muccc/WomoLIN/Doc/freeplan/system_benutzerschnittstellen_v1.0.png

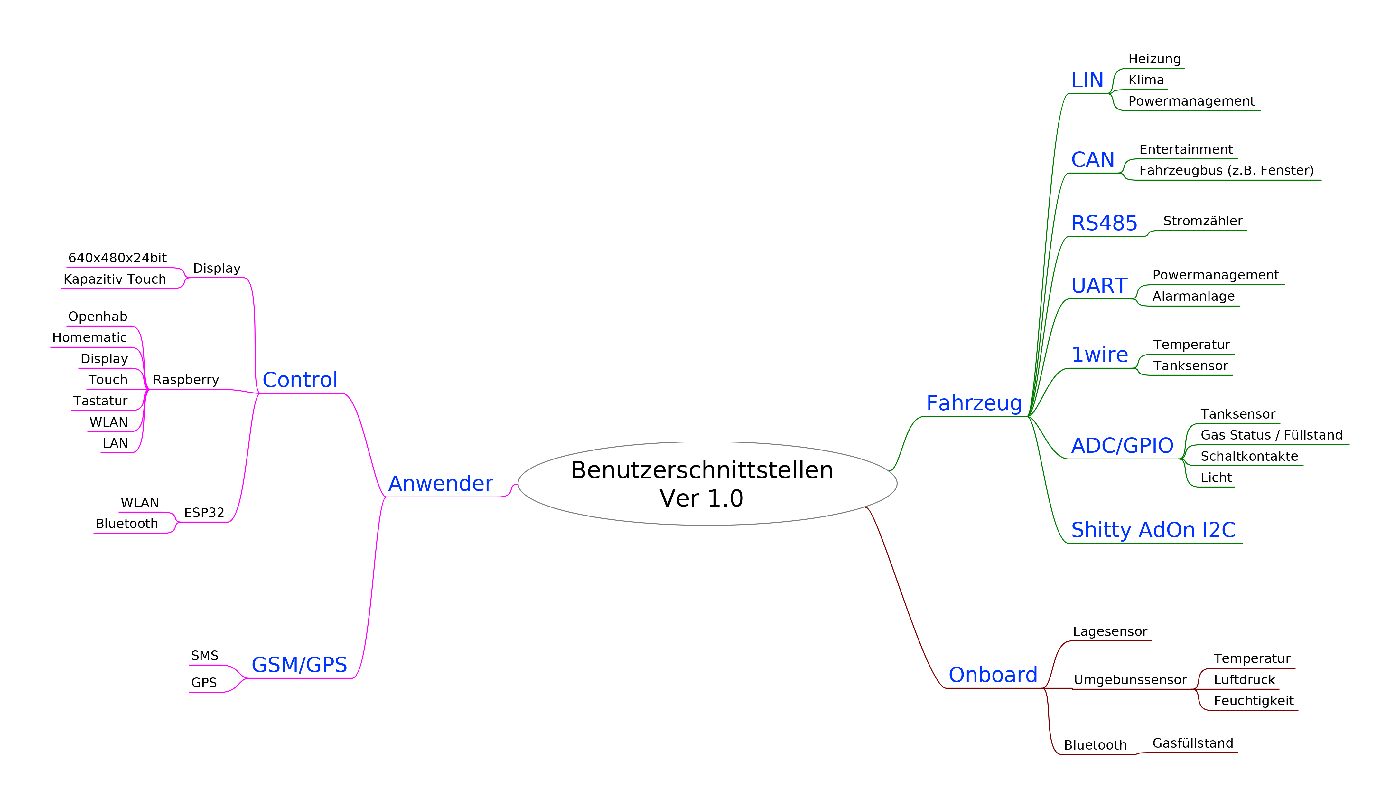
Doc/freeplan/system_benutzerschnittstellen_v1.0.png
