muccc/WomoLIN/Doc/pics/control_sensorboard_cutted.jpg

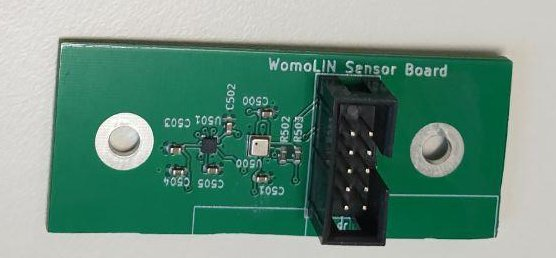
Doc/pics/control_sensorboard_cutted.jpg
