muccc/WomoLIN/Doc/pics/controlboard_2.0_steckverbinder.jpg

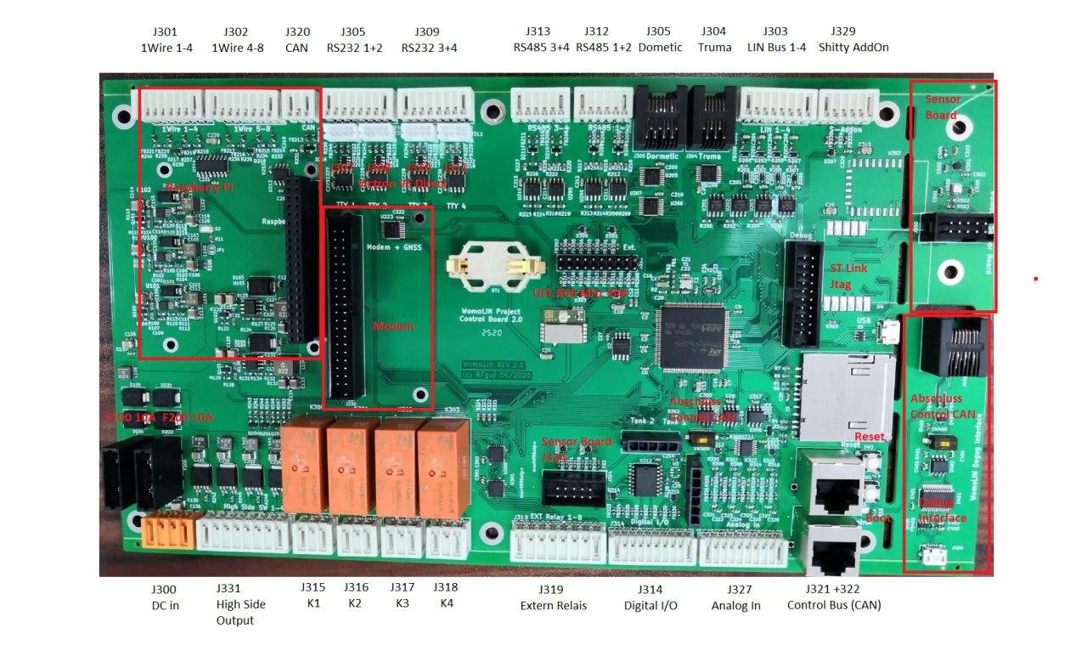
Doc/pics/controlboard_2.0_steckverbinder.jpg
