muccc/WomoLIN/Hardware/Biblotheken/WAGO/3D-Modelle/WAGO Klemmleisten Hebel/WAGO_Klemmleiste_Hebel4Vertikal_RM5mm_2-10-pol/2604-3106/2604-3106.stp

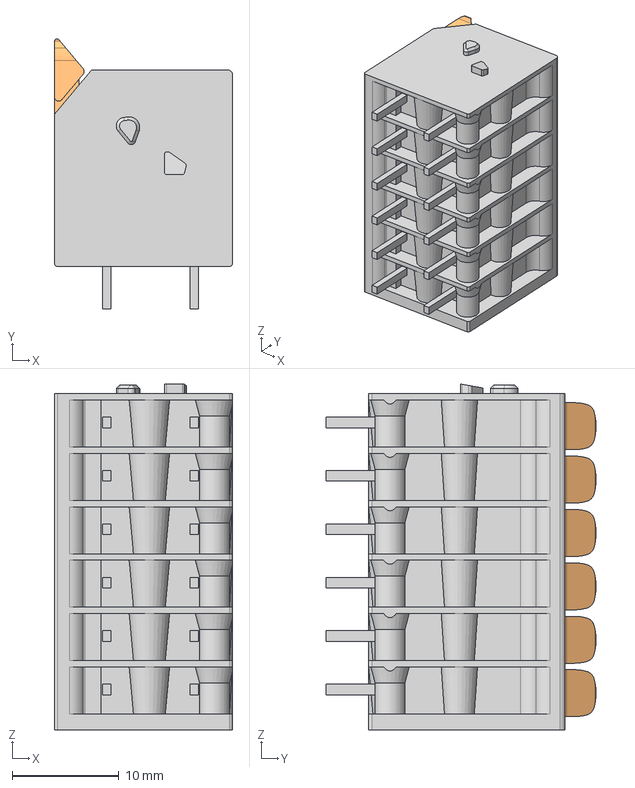
[picture p36: CAD file, 2019-05-10]
Hardware/Biblotheken/WAGO/3D-Modelle/WAGO Klemmleisten Hebel/WAGO_Klemmleiste_Hebel4Vertikal_RM5mm_2-10-pol/2604-3106/2604-3106.stp
16.7 x 25.3 x 32.4 mm
