muccc/WomoLIN/Hardware/Biblotheken/WAGO/3D-Modelle/WAGO Klemmleisten Hebel/WAGO_Klemmleiste_Hebel4Vertikal_RM5mm_2-10-pol/2604-3108/2604-3108.stp

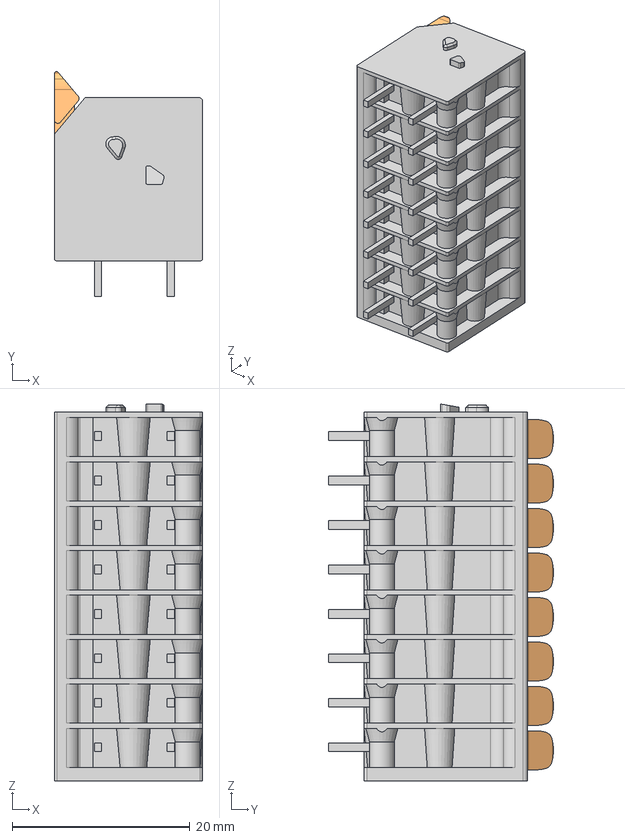
[picture p37: CAD file, 2019-05-10]
Hardware/Biblotheken/WAGO/3D-Modelle/WAGO Klemmleisten Hebel/WAGO_Klemmleiste_Hebel4Vertikal_RM5mm_2-10-pol/2604-3108/2604-3108.stp
16.7 x 25.3 x 42.4 mm
