muccc/WomoLIN/Hardware/Biblotheken/WAGO/3D-Modelle/WAGO Klemmleisten Hebel/WAGO_Klemmleiste_Hebel4Vertikal_RM7,5mm_2-10-pol/2604-3302/2604-3302.stp

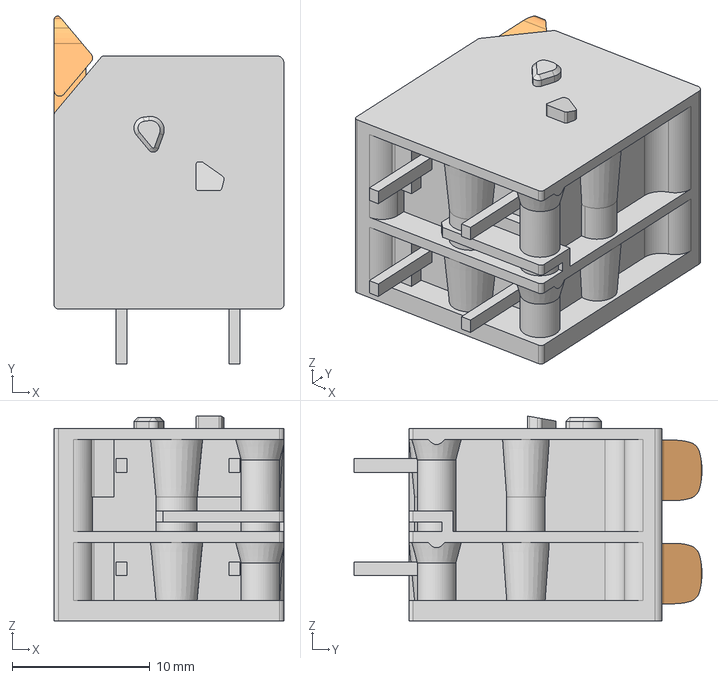
[picture p39: CAD file, 2019-05-10]
Hardware/Biblotheken/WAGO/3D-Modelle/WAGO Klemmleisten Hebel/WAGO_Klemmleiste_Hebel4Vertikal_RM7,5mm_2-10-pol/2604-3302/2604-3302.stp
16.7 x 25.3 x 14.9 mm
