muccc/WomoLIN/Hardware/Biblotheken/WAGO/3D-Modelle/WAGO Klemmleisten Hebel/WAGO_Klemmleiste_Hebel4Vertikal_RM7,5mm_2-10-pol/2604-3303/2604-3303.stp

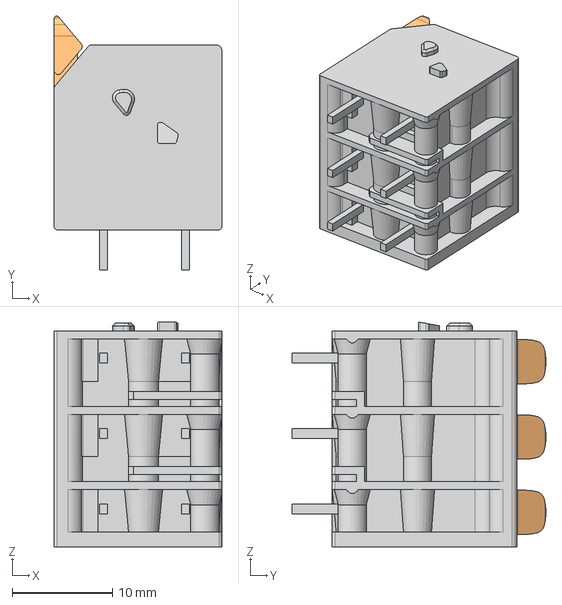
[picture p40: CAD file, 2019-05-10]
Hardware/Biblotheken/WAGO/3D-Modelle/WAGO Klemmleisten Hebel/WAGO_Klemmleiste_Hebel4Vertikal_RM7,5mm_2-10-pol/2604-3303/2604-3303.stp
16.7 x 25.3 x 22.4 mm
