muccc/WomoLIN/Hardware/Biblotheken/WAGO/3D-Modelle/WAGO Klemmleisten Hebel/WAGO_Klemmleiste_Hebel4Vertikal_RM7,5mm_2-10-pol/2604-3304/2604-3304.stp

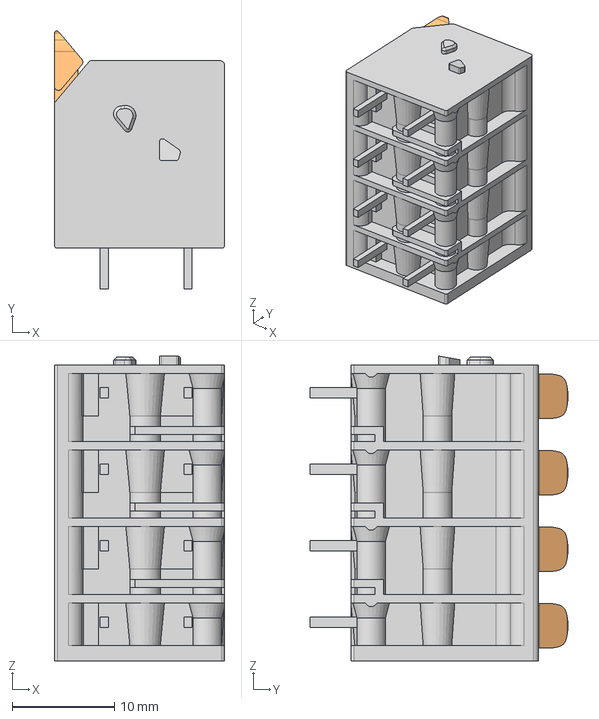
[picture p41: CAD file, 2019-05-10]
Hardware/Biblotheken/WAGO/3D-Modelle/WAGO Klemmleisten Hebel/WAGO_Klemmleiste_Hebel4Vertikal_RM7,5mm_2-10-pol/2604-3304/2604-3304.stp
16.7 x 25.3 x 29.9 mm
