muccc/WomoLIN/Hardware/Biblotheken/WAGO/3D-Modelle/WAGO Klemmleisten Hebel/WAGO_Klemmleiste_Hebel4Vertikal_RM7,5mm_2-10-pol/2604-3306/2604-3306.stp

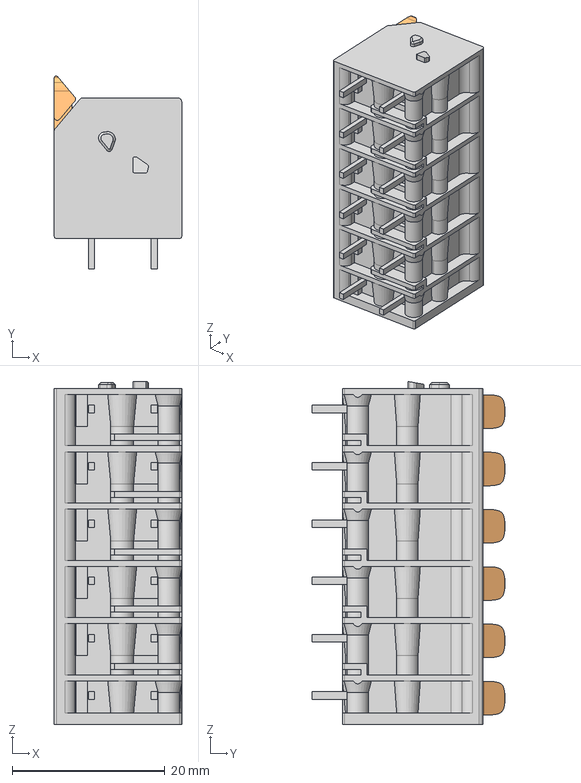
[picture p42: CAD file, 2019-05-10]
Hardware/Biblotheken/WAGO/3D-Modelle/WAGO Klemmleisten Hebel/WAGO_Klemmleiste_Hebel4Vertikal_RM7,5mm_2-10-pol/2604-3306/2604-3306.stp
16.7 x 25.3 x 44.9 mm
