muccc/WomoLIN/Hardware/Biblotheken/WAGO/3D-Modelle/WAGO Klemmleisten Hebel/WAGO_Klemmleiste_Hebel4Vertikal_RM7,5mm_2-10-pol/2604-3308/2604-3308.stp

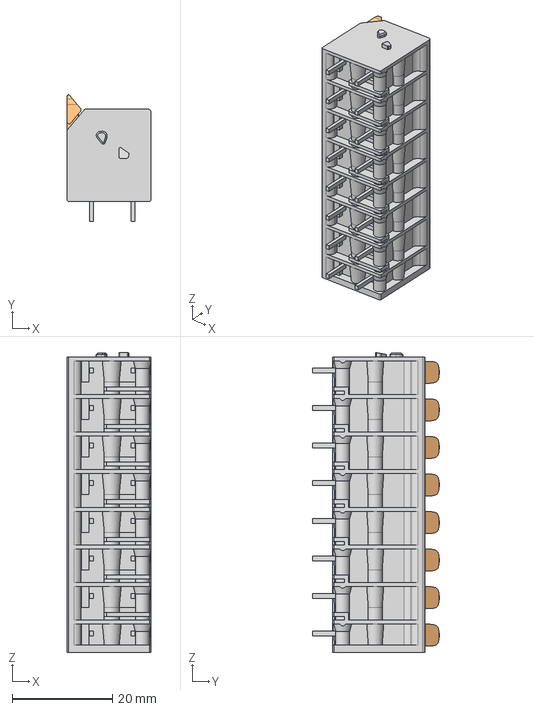
[picture p43: CAD file, 2019-05-10]
Hardware/Biblotheken/WAGO/3D-Modelle/WAGO Klemmleisten Hebel/WAGO_Klemmleiste_Hebel4Vertikal_RM7,5mm_2-10-pol/2604-3308/2604-3308.stp
16.7 x 25.3 x 59.9 mm
