muccc/WomoLIN/Hardware/Biblotheken/WAGO/3D-Modelle/WAGO Klemmleisten Hebel/WAGO_Klemmleiste_Hebel6Horizontal_RM7,5mm_2-10-pol/2606-1103_020-000/2606-1103_020-000.stp

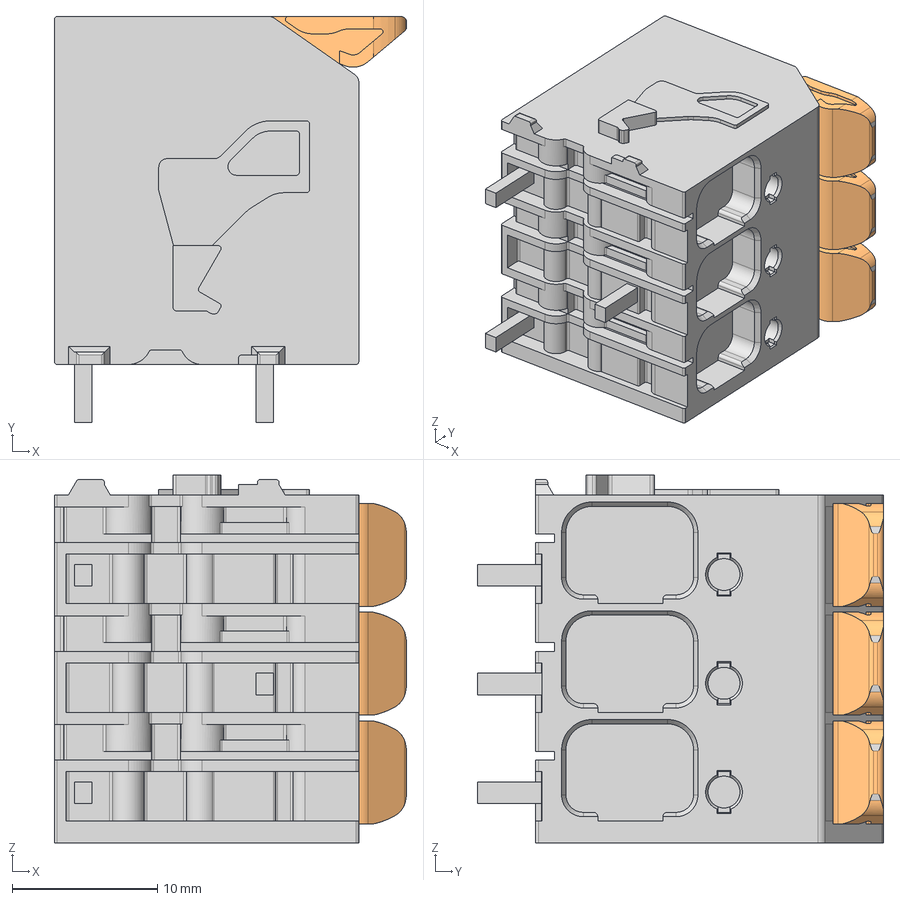
[picture p46: CAD file, 2019-05-10]
Hardware/Biblotheken/WAGO/3D-Modelle/WAGO Klemmleisten Hebel/WAGO_Klemmleiste_Hebel6Horizontal_RM7,5mm_2-10-pol/2606-1103_020-000/2606-1103_020-000.stp
24.3 x 28.0 x 25.4 mm
