muccc/WomoLIN/Hardware/Biblotheken/WAGO/3D-Modelle/WAGO Klemmleisten Hebel/WAGO_Klemmleiste_Hebel6Vertikal_RM7,5mm_2-10-pol/2606-3102_020-000/2606-3102_020-000.stp

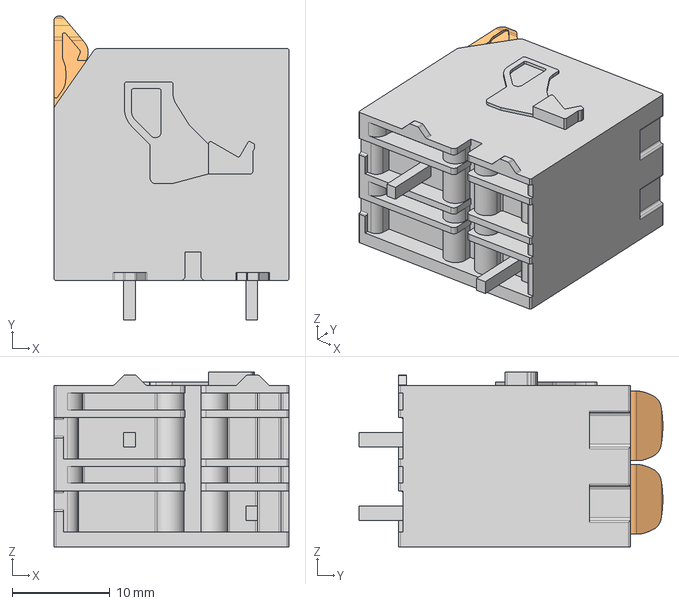
[picture p49: CAD file, 2019-05-10]
Hardware/Biblotheken/WAGO/3D-Modelle/WAGO Klemmleisten Hebel/WAGO_Klemmleiste_Hebel6Vertikal_RM7,5mm_2-10-pol/2606-3102_020-000/2606-3102_020-000.stp
24.0 x 31.0 x 17.9 mm
