muccc/WomoLIN/Hardware/Biblotheken/WAGO/3D-Modelle/WAGO Klemmleisten Hebel/WAGO_Klemmleiste_Hebel6Vertikal_RM7,5mm_2-10-pol/2606-3103_020-000/2606-3103_020-000.stp

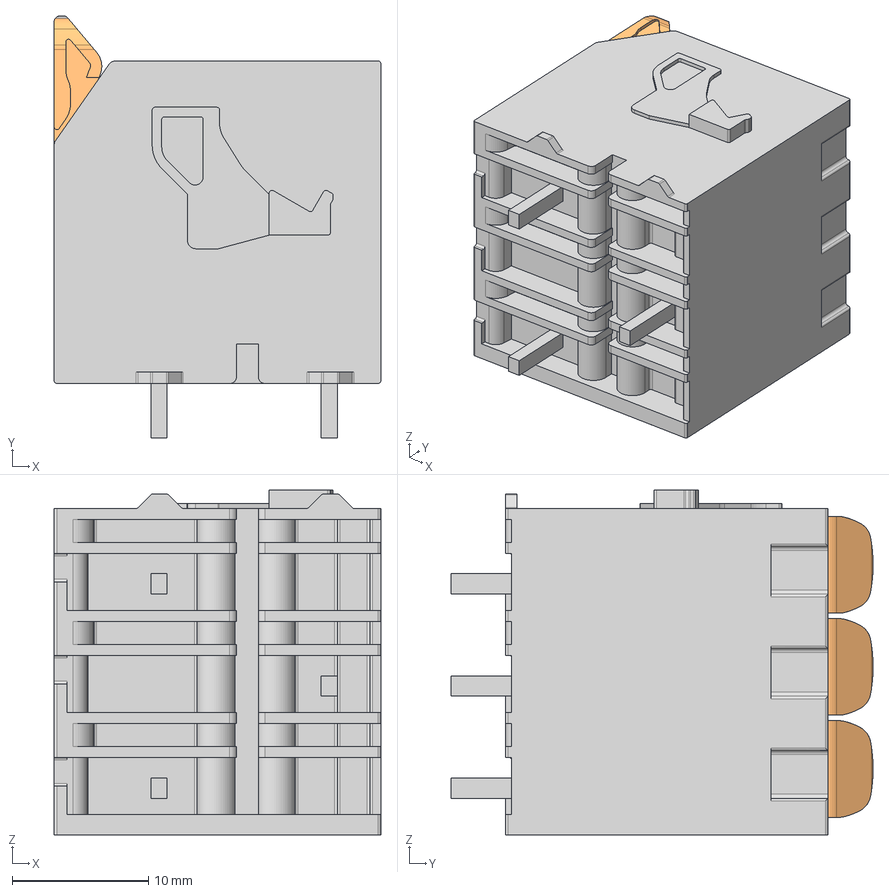
[picture p50: CAD file, 2019-05-10]
Hardware/Biblotheken/WAGO/3D-Modelle/WAGO Klemmleisten Hebel/WAGO_Klemmleiste_Hebel6Vertikal_RM7,5mm_2-10-pol/2606-3103_020-000/2606-3103_020-000.stp
24.0 x 31.0 x 25.4 mm
