muccc/WomoLIN/Hardware/Biblotheken/RS SMD/3D-Modelle/SMD RCL/C_0805.stp

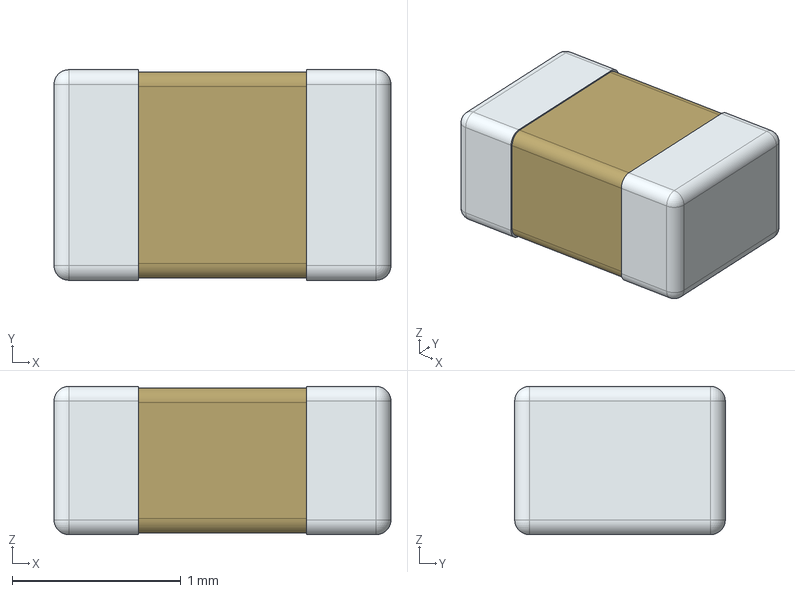
[picture p53: CAD file, 2019-05-28]
Hardware/Biblotheken/RS SMD/3D-Modelle/SMD RCL/C_0805.stp
2.00 x 1.25 x 0.88 mm
