muccc/WomoLIN/Hardware/Biblotheken/WAGO/3D-Modelle/734-264.stp

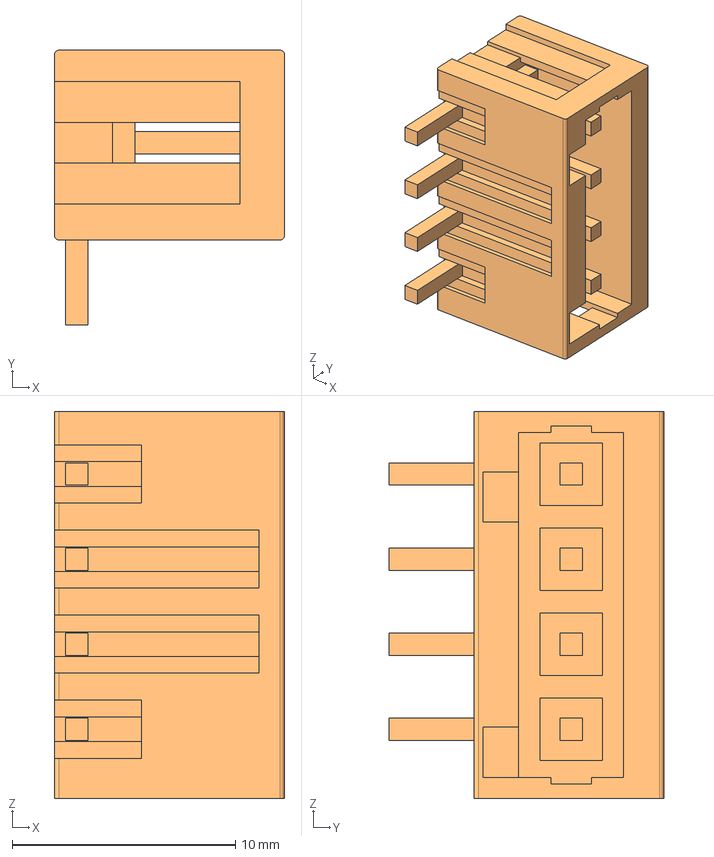
[picture p54: CAD file, 2019-10-14]
Hardware/Biblotheken/WAGO/3D-Modelle/734-264.stp
10.3 x 12.3 x 17.3 mm
