muccc/WomoLIN/Hardware/Biblotheken/RS SMD/3D-Modelle/SMD RCL/C_0402.stp

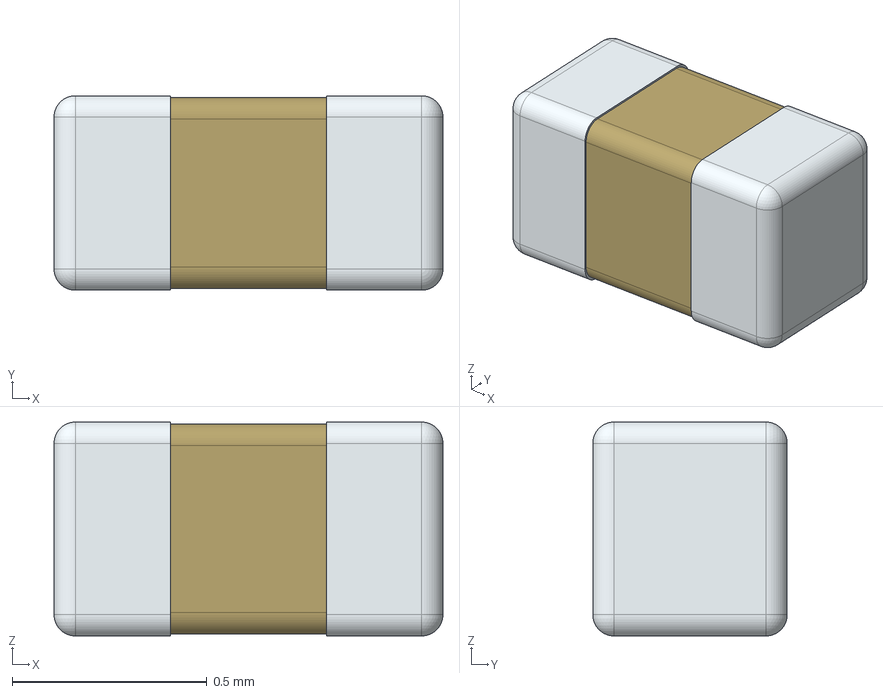
[picture p55: CAD file, 2019-05-28]
Hardware/Biblotheken/RS SMD/3D-Modelle/SMD RCL/C_0402.stp
1.00 x 0.5 x 0.55 mm
