muccc/WomoLIN/Hardware/Biblotheken/WAGO/3D-Modelle/733-363.stp

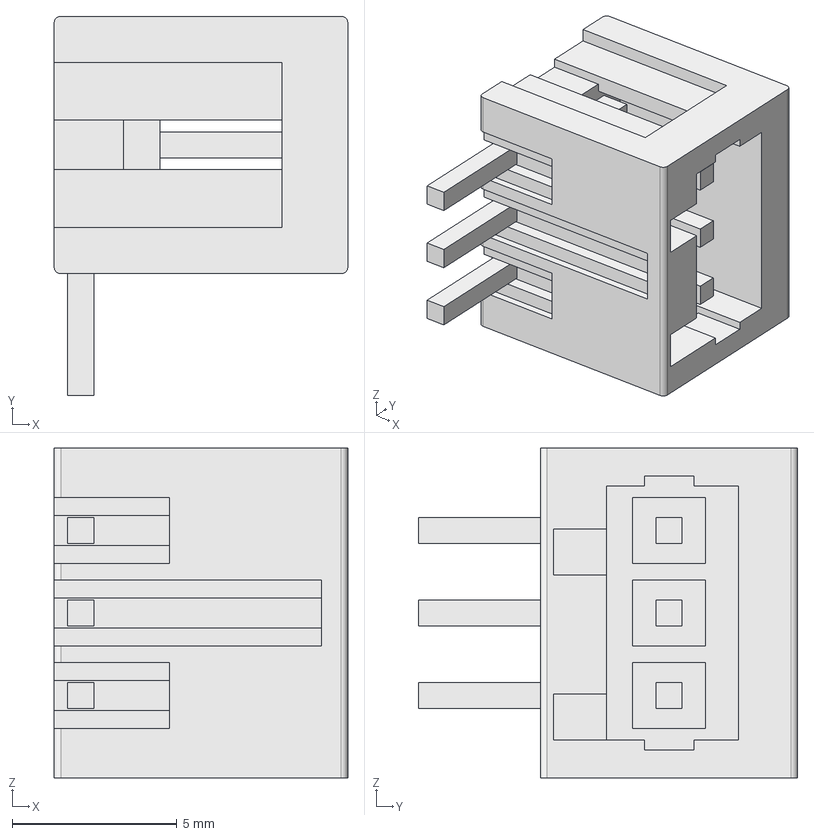
[picture p56: CAD file, 2019-10-14]
Hardware/Biblotheken/WAGO/3D-Modelle/733-363.stp
8.90 x 11.5 x 10.0 mm
