muccc/WomoLIN/Hardware/Biblotheken/RS SMD/3D-Modelle/SMD RCL/C_0603.stp

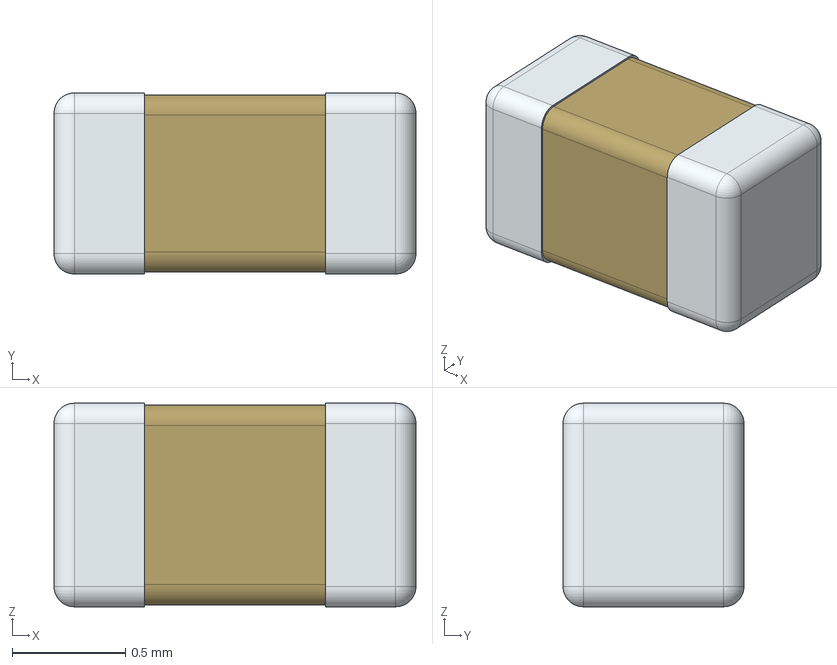
[picture p57: CAD file, 2019-05-28]
Hardware/Biblotheken/RS SMD/3D-Modelle/SMD RCL/C_0603.stp
1.60 x 0.8 x 0.9 mm
