muccc/WomoLIN/Hardware/Biblotheken/WAGO/3D-Modelle/734-164.stp

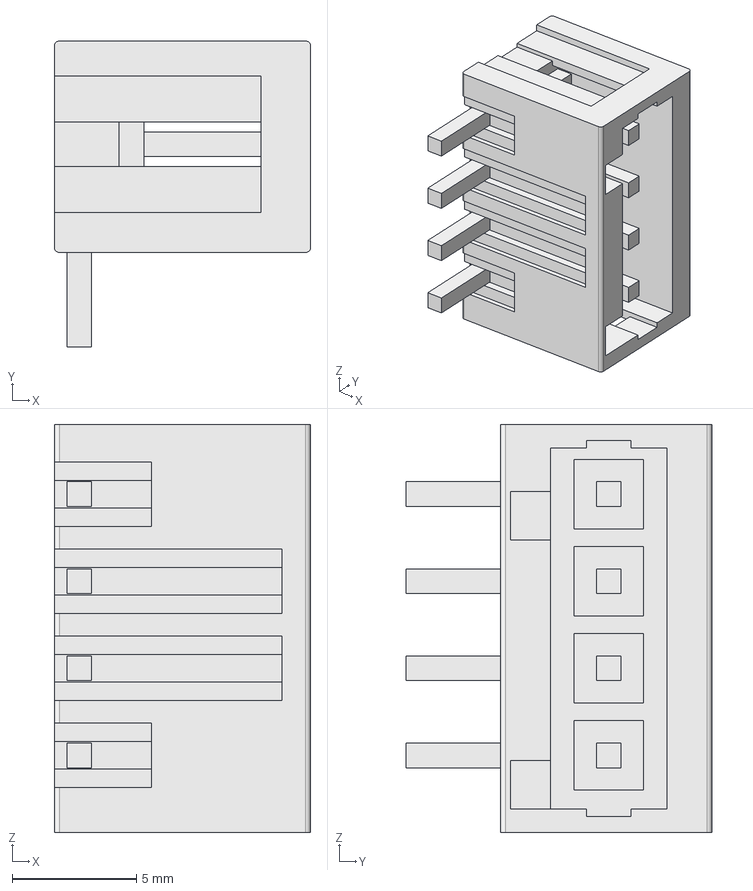
[picture p58: CAD file, 2019-10-14]
Hardware/Biblotheken/WAGO/3D-Modelle/734-164.stp
10.3 x 12.3 x 16.4 mm
