muccc/WomoLIN/Hardware/Biblotheken/RS SMD/3D-Modelle/SMD RCL/L_0603.step

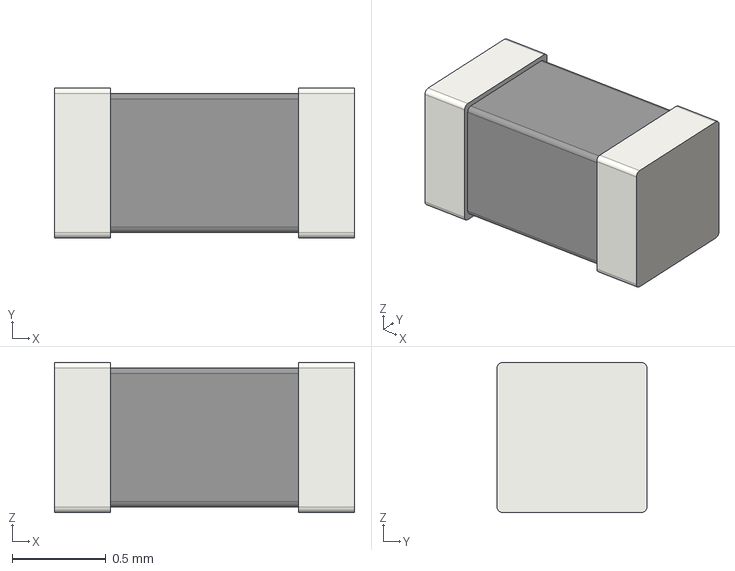
[picture p59: CAD file, 2019-05-28]
Hardware/Biblotheken/RS SMD/3D-Modelle/SMD RCL/L_0603.step
1.60 x 0.8 x 0.8 mm
