muccc/WomoLIN/Hardware/Biblotheken/WAGO/3D-Modelle/733-366.stp

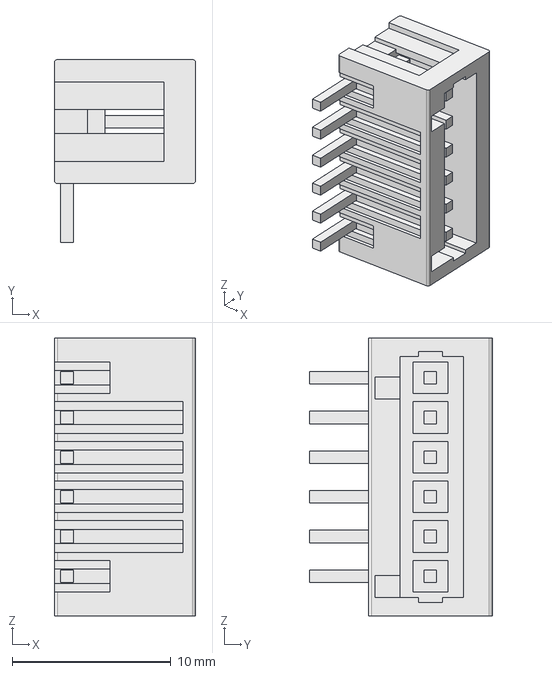
[picture p60: CAD file, 2019-10-14]
Hardware/Biblotheken/WAGO/3D-Modelle/733-366.stp
8.90 x 11.5 x 17.5 mm
