muccc/WomoLIN/Hardware/Biblotheken/RS SMD/3D-Modelle/SMD RCL/0805.stp

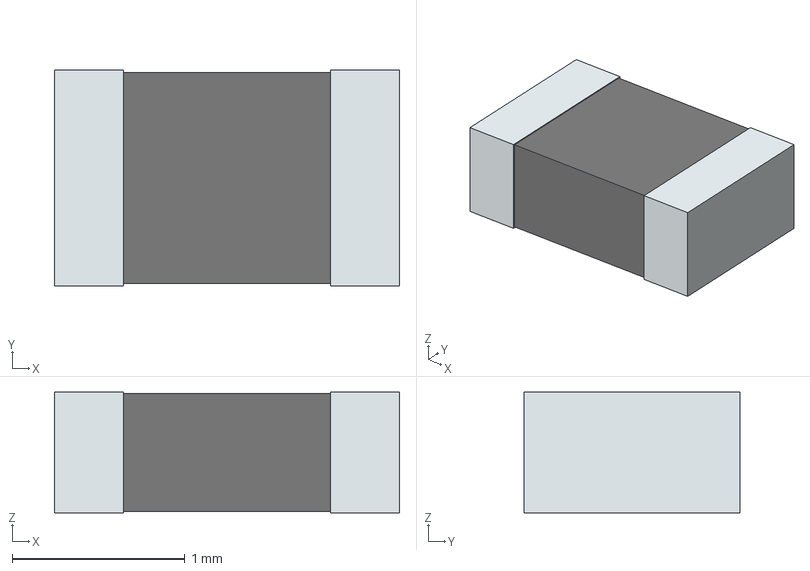
[picture p61: CAD file, 2019-05-28]
Hardware/Biblotheken/RS SMD/3D-Modelle/SMD RCL/0805.stp
2.00 x 1.25 x 0.7 mm
term1
term2
