muccc/WomoLIN/Hardware/Biblotheken/WAGO/3D-Modelle/733-368.stp

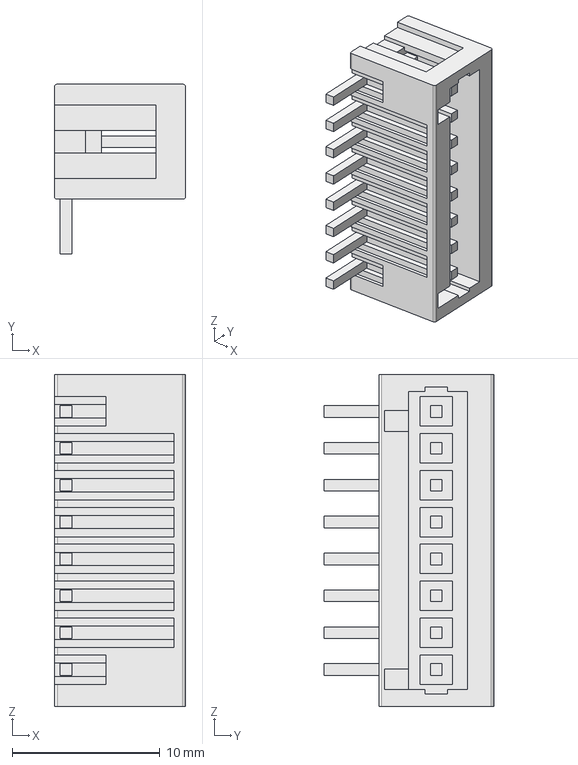
[picture p62: CAD file, 2019-10-14]
Hardware/Biblotheken/WAGO/3D-Modelle/733-368.stp
8.90 x 11.5 x 22.5 mm
