muccc/WomoLIN/Hardware/Biblotheken/RS SMD/3D-Modelle/SMD RCL/C_0201.stp

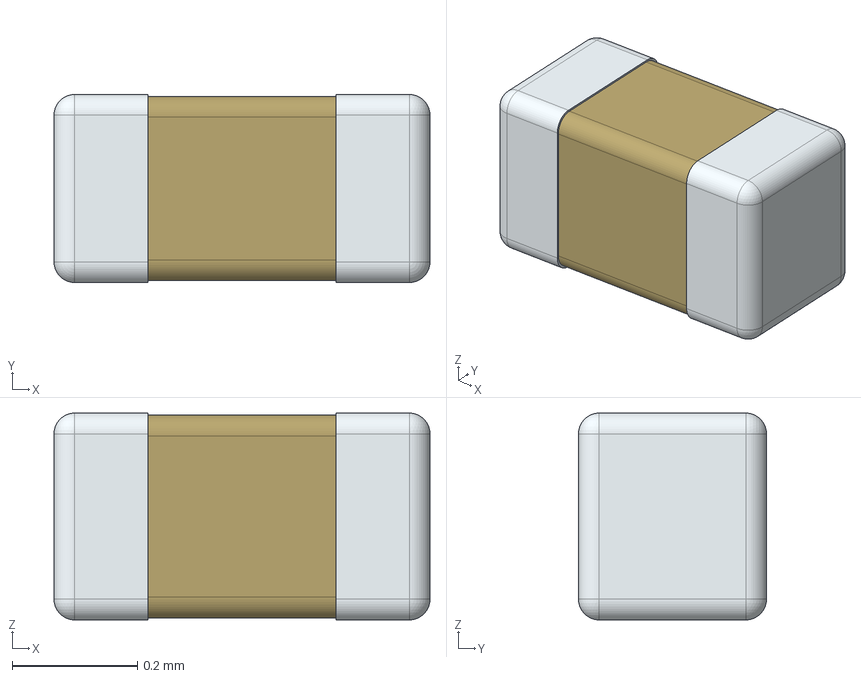
[picture p63: CAD file, 2019-05-28]
Hardware/Biblotheken/RS SMD/3D-Modelle/SMD RCL/C_0201.stp
0.6 x 0.3 x 0.33 mm
