muccc/WomoLIN/Hardware/Biblotheken/WAGO/3D-Modelle/250-203.stp

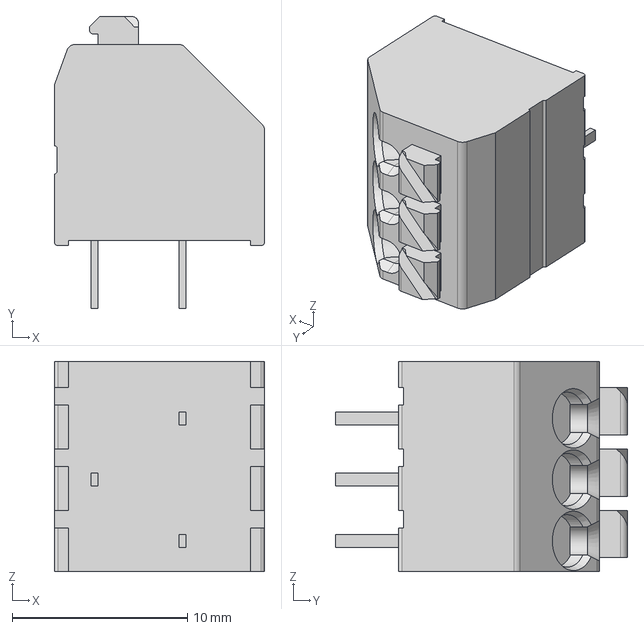
[picture p64: CAD file, 2019-04-16]
Hardware/Biblotheken/WAGO/3D-Modelle/250-203.stp
12.0 x 16.7 x 12.0 mm
