muccc/WomoLIN/Hardware/Biblotheken/WAGO/3D-Modelle/250-208.stp

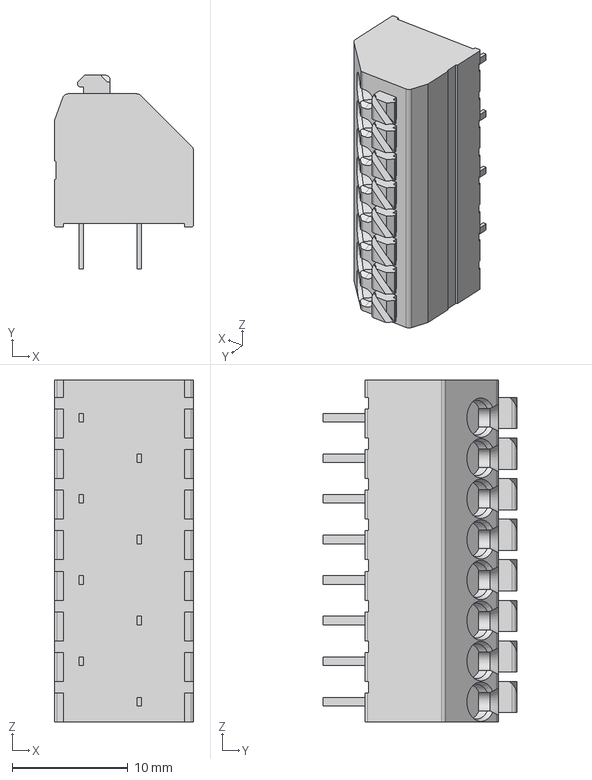
[picture p66: CAD file, 2019-04-16]
Hardware/Biblotheken/WAGO/3D-Modelle/250-208.stp
12.0 x 16.7 x 29.5 mm
