muccc/WomoLIN/Hardware/Biblotheken/WAGO/3D-Modelle/250-502.stp

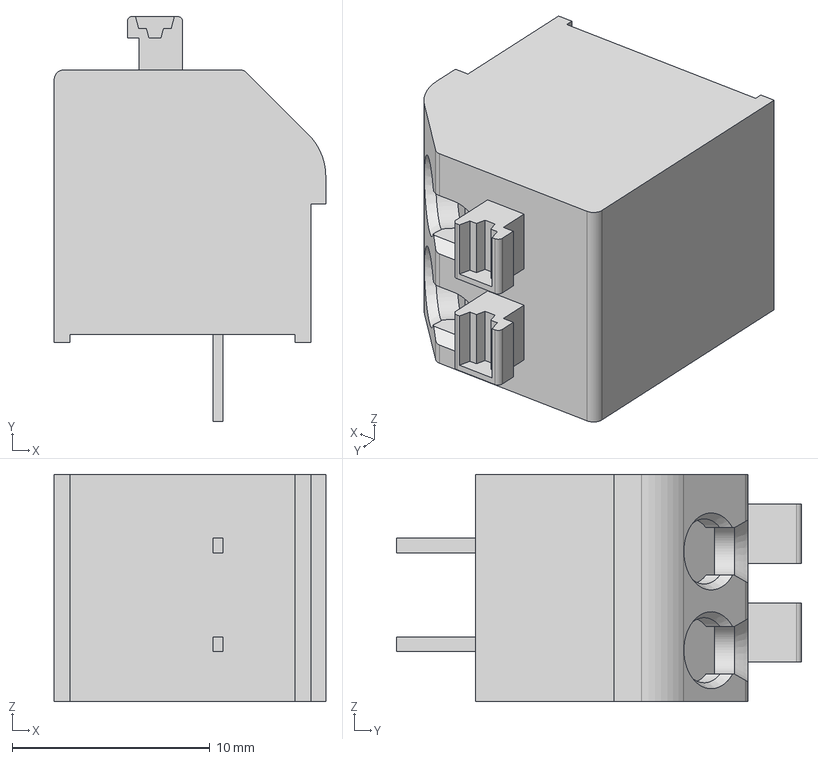
[picture p68: CAD file, 2019-04-16]
Hardware/Biblotheken/WAGO/3D-Modelle/250-502.stp
13.8 x 20.5 x 11.5 mm
