muccc/WomoLIN/Hardware/Biblotheken/RS SMD/3D-Modelle/SMD RCL/1206.stp

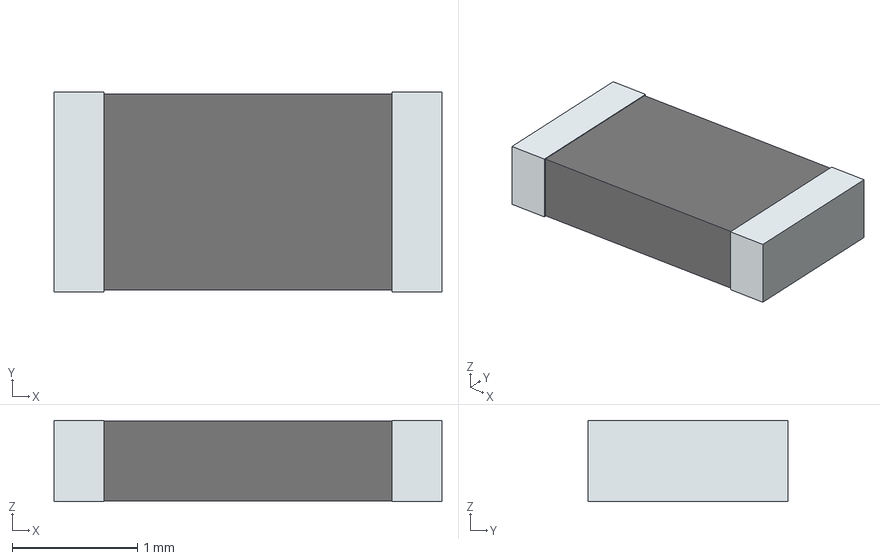
[picture p69: CAD file, 2019-05-28]
Hardware/Biblotheken/RS SMD/3D-Modelle/SMD RCL/1206.stp
3.10 x 1.60 x 0.65 mm
term1
term2
