muccc/WomoLIN/Hardware/Biblotheken/WAGO/3D-Modelle/250-508.stp

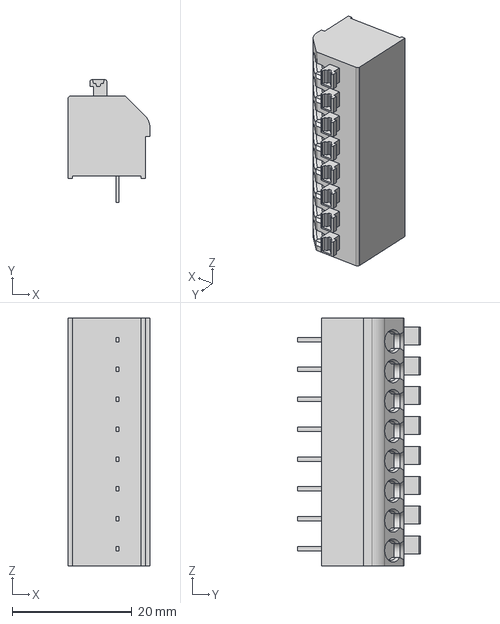
[picture p70: CAD file, 2019-04-16]
Hardware/Biblotheken/WAGO/3D-Modelle/250-508.stp
13.8 x 20.5 x 41.5 mm
