muccc/WomoLIN/Hardware/Biblotheken/WAGO/3D-Modelle/250-510.stp

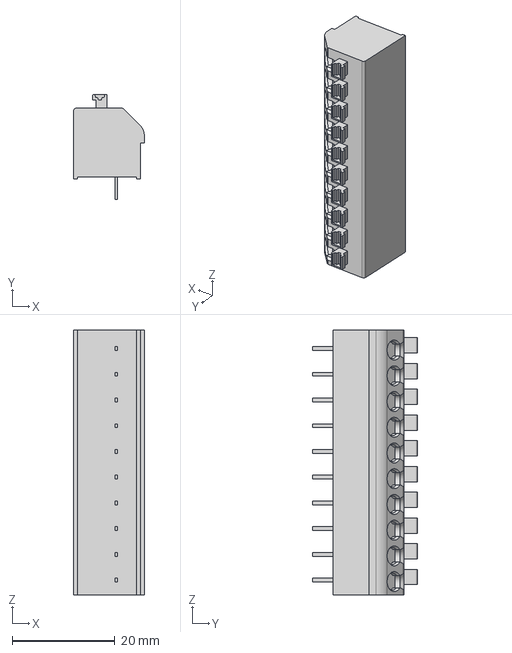
[picture p72: CAD file, 2019-04-16]
Hardware/Biblotheken/WAGO/3D-Modelle/250-510.stp
13.8 x 20.5 x 51.5 mm
