muccc/WomoLIN/Hardware/Biblotheken/RS SMD/3D-Modelle/SMD RCL/0603.stp

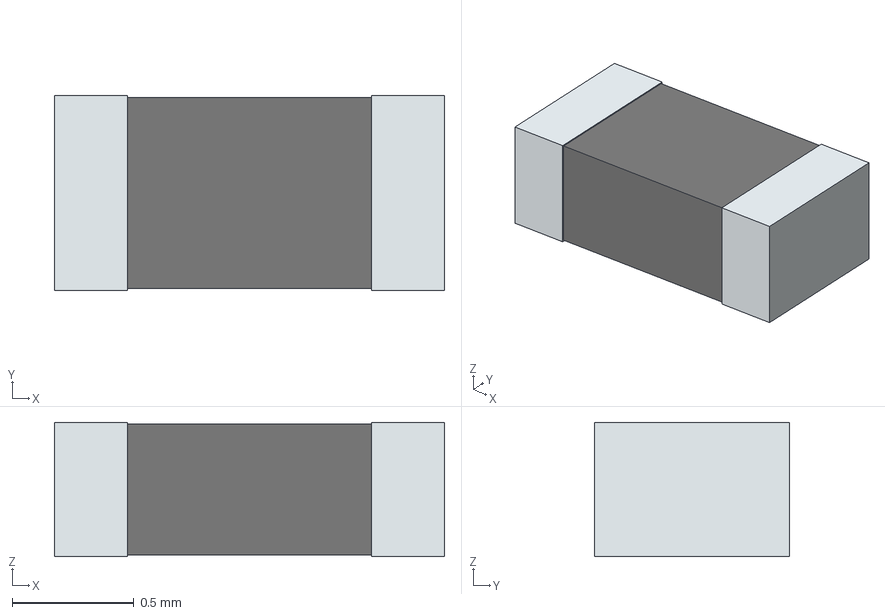
[picture p73: CAD file, 2019-05-28]
Hardware/Biblotheken/RS SMD/3D-Modelle/SMD RCL/0603.stp
1.60 x 0.8 x 0.55 mm
term1
term2
