muccc/WomoLIN/Hardware/Biblotheken/WAGO/3D-Modelle/250-210.stp

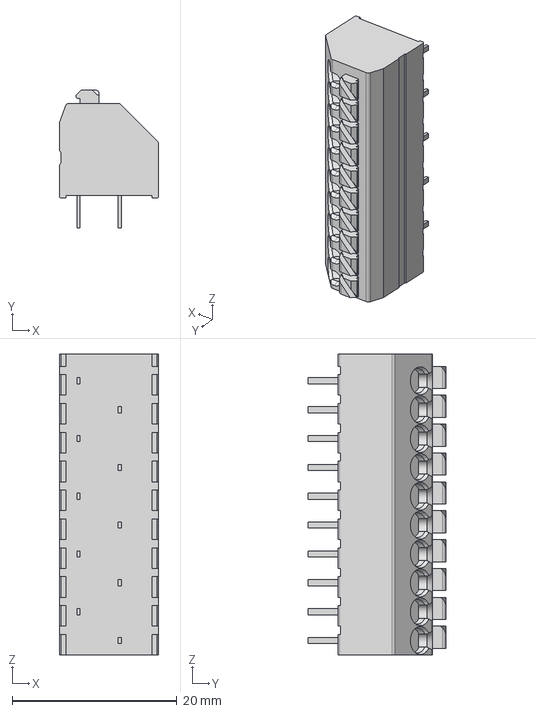
[picture p74: CAD file, 2019-04-16]
Hardware/Biblotheken/WAGO/3D-Modelle/250-210.stp
12.0 x 16.7 x 36.5 mm
