muccc/WomoLIN/Hardware/Biblotheken/WAGO/3D-Modelle/250-504.stp

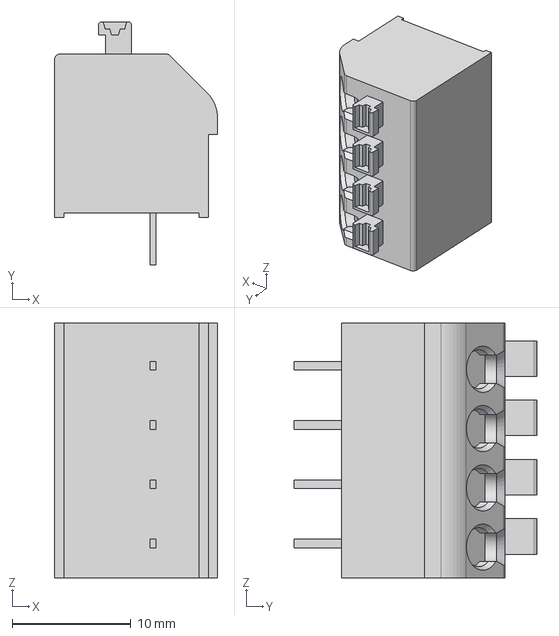
[picture p76: CAD file, 2019-04-16]
Hardware/Biblotheken/WAGO/3D-Modelle/250-504.stp
13.8 x 20.5 x 21.5 mm
