muccc/WomoLIN/Hardware/Biblotheken/RS SMD/3D-Modelle/SMD RCL/C_1206.stp

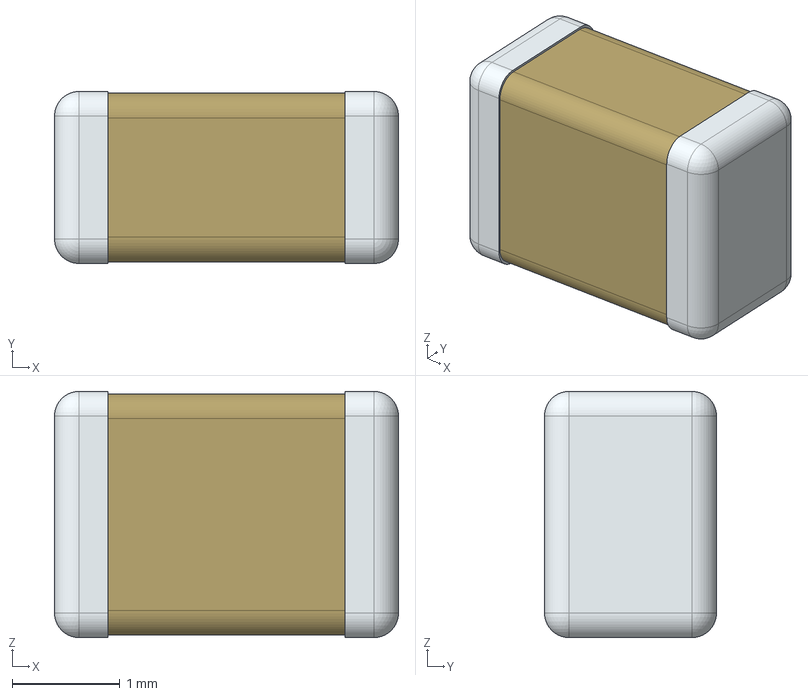
[picture p77: CAD file, 2019-05-28]
Hardware/Biblotheken/RS SMD/3D-Modelle/SMD RCL/C_1206.stp
3.20 x 1.60 x 2.29 mm
