muccc/WomoLIN/Hardware/Biblotheken/WAGO/3D-Modelle/250-204.stp

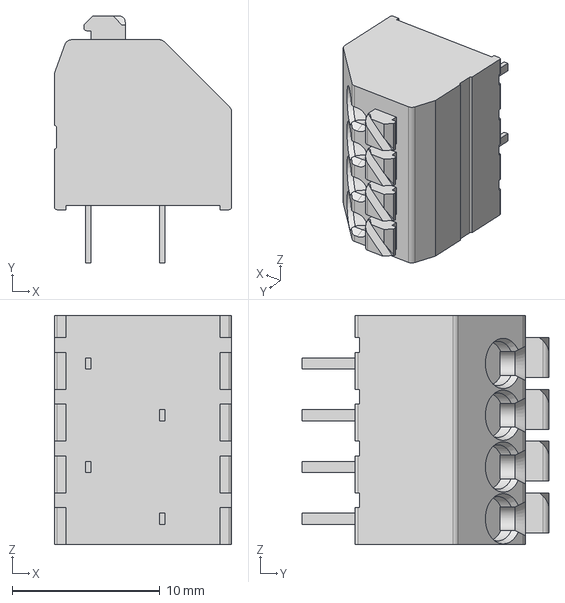
[picture p78: CAD file, 2019-04-16]
Hardware/Biblotheken/WAGO/3D-Modelle/250-204.stp
12.0 x 16.7 x 15.5 mm
