muccc/WomoLIN/Hardware/Biblotheken/WAGO/3D-Modelle/250-602.stp

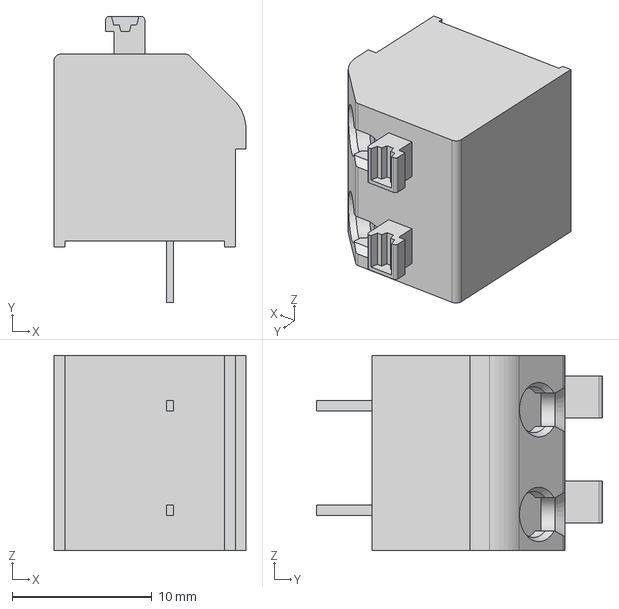
[picture p80: CAD file, 2019-04-16]
Hardware/Biblotheken/WAGO/3D-Modelle/250-602.stp
13.8 x 20.5 x 14.0 mm
