muccc/WomoLIN/Hardware/Biblotheken/WAGO/3D-Modelle/250-506.stp

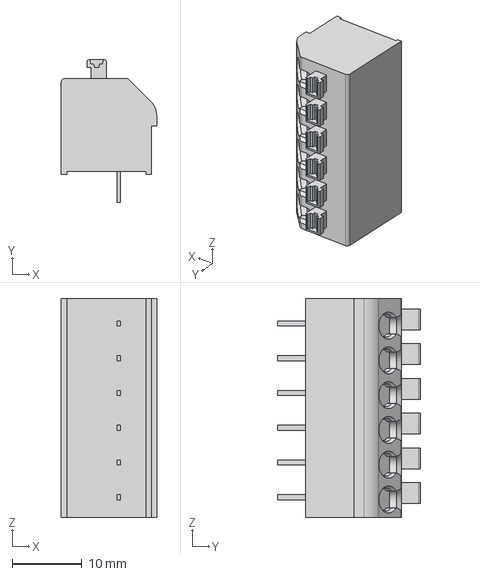
[picture p81: CAD file, 2019-04-16]
Hardware/Biblotheken/WAGO/3D-Modelle/250-506.stp
13.8 x 20.5 x 31.5 mm
