muccc/WomoLIN/Hardware/Biblotheken/WAGO/3D-Modelle/250-604.stp

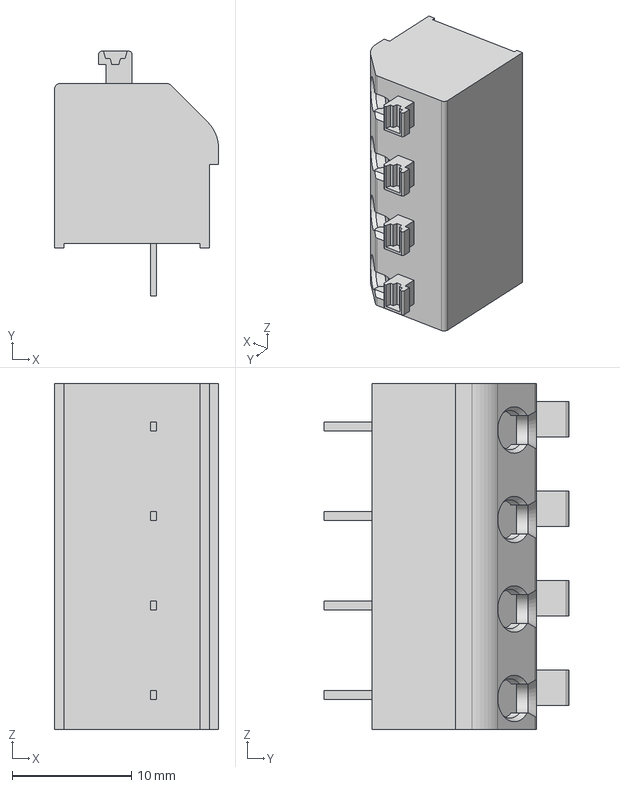
[picture p82: CAD file, 2019-04-16]
Hardware/Biblotheken/WAGO/3D-Modelle/250-604.stp
13.8 x 20.5 x 29.0 mm
