muccc/WomoLIN/Hardware/Biblotheken/WAGO/3D-Modelle/250-503.stp

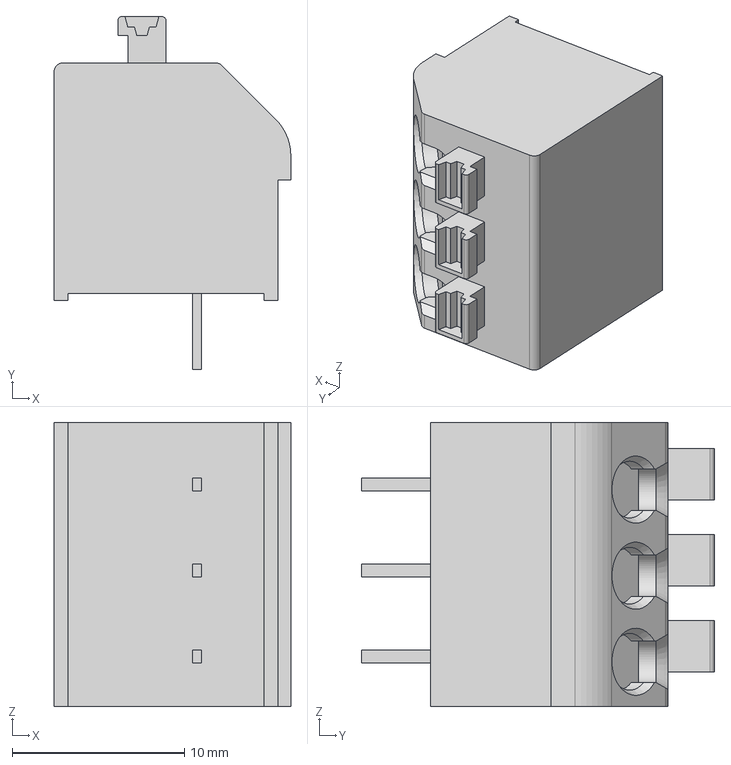
[picture p83: CAD file, 2019-04-16]
Hardware/Biblotheken/WAGO/3D-Modelle/250-503.stp
13.8 x 20.5 x 16.5 mm
