muccc/WomoLIN/Hardware/Biblotheken/WAGO/3D-Modelle/250-206.stp

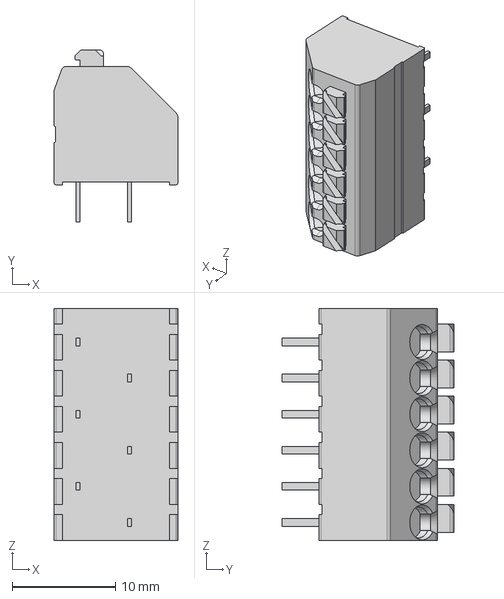
[picture p84: CAD file, 2019-04-16]
Hardware/Biblotheken/WAGO/3D-Modelle/250-206.stp
12.0 x 16.7 x 22.5 mm
