muccc/WomoLIN/Hardware/Biblotheken/WAGO/3D-Modelle/250-202.stp

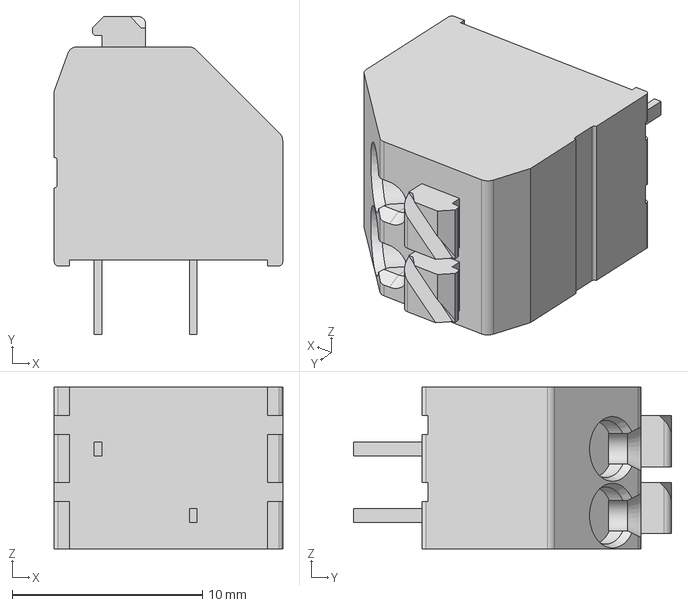
[picture p85: CAD file, 2019-04-16]
Hardware/Biblotheken/WAGO/3D-Modelle/250-202.stp
12.0 x 16.7 x 8.50 mm
