muccc/WomoLIN/Hardware/Biblotheken/WAGO/3D-Modelle/250-606.stp

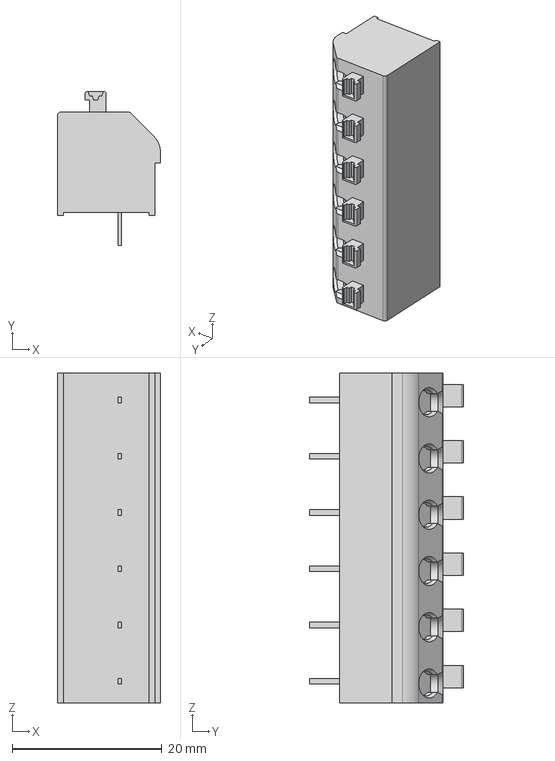
[picture p86: CAD file, 2019-04-16]
Hardware/Biblotheken/WAGO/3D-Modelle/250-606.stp
13.8 x 20.5 x 44.0 mm
