muccc/WomoLIN/Hardware/Biblotheken/WAGO/3D-Modelle/250-608.stp

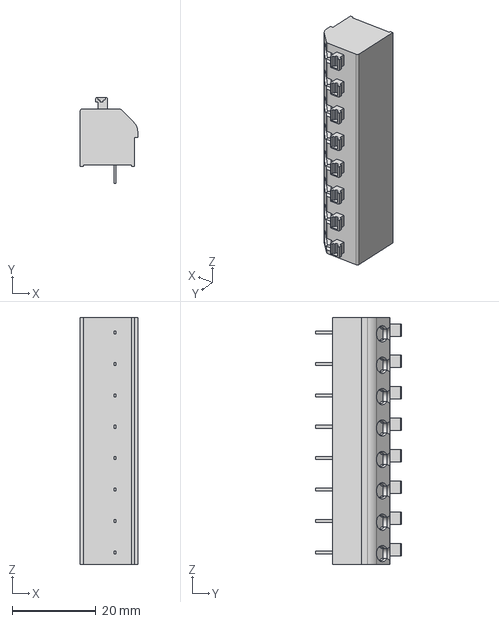
[picture p87: CAD file, 2019-04-16]
Hardware/Biblotheken/WAGO/3D-Modelle/250-608.stp
13.8 x 20.5 x 59.0 mm
