muccc/WomoLIN/Hardware/Biblotheken/WAGO/3D-Modelle/250-610.stp

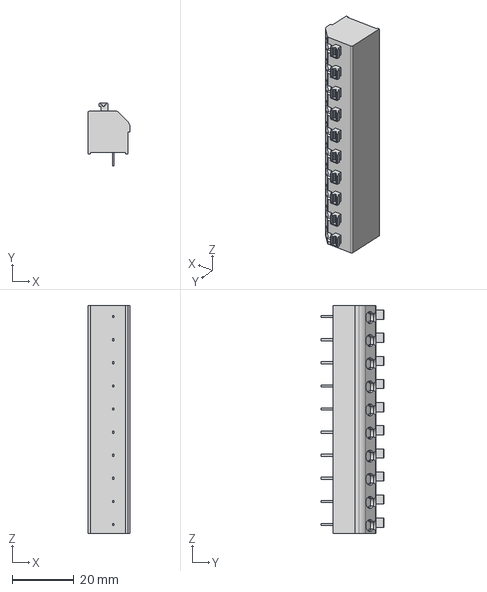
[picture p88: CAD file, 2019-04-16]
Hardware/Biblotheken/WAGO/3D-Modelle/250-610.stp
13.8 x 20.5 x 74.0 mm
